TheDocotor/Senior-Project/SerialSensorData/Ellip_test6_serial.csv

PC_Timestamp | Device_Time_ms | LevelX | LevelY | inputVoltageX | inputVoltageY | inputVoltageSUM
2025-04-04T18:02:12.944549 | 154919 | 0.000 | 0.000 | 0.101 | 0.216 | 3.193
2025-04-04T18:02:13.694333 | 155670 | 0.101 | 0.216 | 0.100 | 0.215 | 3.194
2025-04-04T18:02:14.445692 | 156421 | 0.101 | 0.216 | 0.100 | 0.215 | 3.193
2025-04-04T18:02:15.196565 | 157171 | 0.101 | 0.216 | 0.100 | 0.215 | 3.193
2025-04-04T18:02:15.947939 | 157922 | 0.101 | 0.216 | 0.099 | 0.215 | 3.193
2025-04-04T18:02:16.698144 | 158673 | 0.101 | 0.216 | 0.103 | 0.217 | 3.192
2025-04-04T18:02:17.449260 | 159424 | 0.101 | 0.216 | 0.101 | 0.216 | 3.193
2025-04-04T18:02:18.198008 | 160175 | 0.101 | 0.216 | 0.102 | 0.216 | 3.193
2025-04-04T18:02:18.951042 | 160926 | 0.101 | 0.216 | 0.101 | 0.215 | 3.193
2025-04-04T18:02:19.700249 | 161677 | 0.101 | 0.216 | 0.100 | 0.215 | 3.193
2025-04-04T18:02:20.452247 | 162428 | 0.101 | 0.216 | 0.101 | 0.215 | 3.192
2025-04-04T18:02:21.203152 | 163178 | 0.101 | 0.216 | 0.101 | 0.215 | 3.193
2025-04-04T18:02:21.953931 | 163929 | 0.101 | 0.216 | 0.101 | 0.215 | 3.194
2025-04-04T18:02:22.704747 | 164680 | 0.101 | 0.216 | 0.101 | 0.214 | 3.192
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
