TheDocotor/Senior-Project/SerialSensorData/Ellip_test8_serial.csv

PC_Timestamp | Device_Time_ms | LevelX | LevelY | inputVoltageX | inputVoltageY | inputVoltageSUM
2025-04-08T15:50:00.214956 | 255589 | 5.330 | 5.940 | 5.331 | 5.947 | 3.181
2025-04-08T15:50:00.963926 | 256340 | 5.330 | 5.940 | 5.332 | 5.944 | 3.181
2025-04-08T15:50:01.716474 | 257090 | 5.330 | 5.940 | 5.333 | 5.948 | 3.181
2025-04-08T15:50:02.466522 | 257841 | 5.330 | 5.940 | 5.338 | 5.953 | 3.183
2025-04-08T15:50:03.218086 | 258592 | 5.330 | 5.940 | 5.345 | 5.953 | 3.183
2025-04-08T15:50:03.969129 | 259343 | 5.330 | 5.940 | 5.328 | 5.946 | 3.183
2025-04-08T15:50:04.718286 | 260093 | 5.330 | 5.940 | 5.336 | 5.950 | 3.184
2025-04-08T15:50:05.470040 | 260844 | 5.330 | 5.940 | 5.337 | 5.952 | 3.185
2025-04-08T15:50:06.219609 | 261595 | 5.330 | 5.940 | 5.328 | 5.944 | 3.184
2025-04-08T15:50:06.970060 | 262345 | 5.330 | 5.940 | 5.338 | 5.953 | 3.186
2025-04-08T15:50:07.722448 | 263096 | 5.330 | 5.940 | 5.337 | 5.953 | 3.186
2025-04-08T15:50:08.473148 | 263847 | 5.330 | 5.940 | 5.348 | 5.959 | 3.186
2025-04-08T15:50:09.223567 | 264597 | 5.330 | 5.940 | 5.332 | 5.949 | 3.186
2025-04-08T15:50:09.972090 | 265348 | 5.330 | 5.940 | 5.339 | 5.954 | 3.187
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
