TheDocotor/Senior-Project/SerialSensorData/Ellip_test9_serial.csv

PC_Timestamp | Device_Time_ms | LevelX | LevelY | inputVoltageX | inputVoltageY | inputVoltageSUM
2025-04-08T16:38:29.570004 | 3165002 | 5.389 | 5.937 | 5.387 | 5.937 | 3.172
2025-04-08T16:38:30.322037 | 3165753 | 5.389 | 5.937 | 5.386 | 5.936 | 3.169
2025-04-08T16:38:31.072890 | 3166503 | 5.389 | 5.937 | 5.386 | 5.933 | 3.171
2025-04-08T16:38:31.822191 | 3167254 | 5.389 | 5.937 | 5.383 | 5.931 | 3.170
2025-04-08T16:38:32.573754 | 3168005 | 5.389 | 5.937 | 5.389 | 5.932 | 3.171
2025-04-08T16:38:33.324326 | 3168756 | 5.389 | 5.937 | 5.392 | 5.938 | 3.170
2025-04-08T16:38:34.075585 | 3169506 | 5.389 | 5.937 | 5.387 | 5.932 | 3.171
2025-04-08T16:38:34.825944 | 3170257 | 5.389 | 5.937 | 5.385 | 5.934 | 3.171
2025-04-08T16:38:35.577055 | 3171008 | 5.389 | 5.937 | 5.389 | 5.937 | 3.170
2025-04-08T16:38:36.327570 | 3171758 | 5.389 | 5.937 | 5.388 | 5.935 | 3.169
2025-04-08T16:38:37.078165 | 3172509 | 5.389 | 5.937 | 5.387 | 5.933 | 3.171
2025-04-08T16:38:37.827852 | 3173260 | 5.389 | 5.937 | 5.388 | 5.934 | 3.168
2025-04-08T16:38:38.579724 | 3174010 | 5.389 | 5.937 | 5.383 | 5.932 | 3.169
2025-04-08T16:38:39.329178 | 3174761 | 5.389 | 5.937 | 5.387 | 5.933 | 3.168
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
